pritikaselvam-svg/NovaB/02_Industrial_Design/Sketches/WhatsApp Image 2026-07-04 at 12.52.29.jpeg

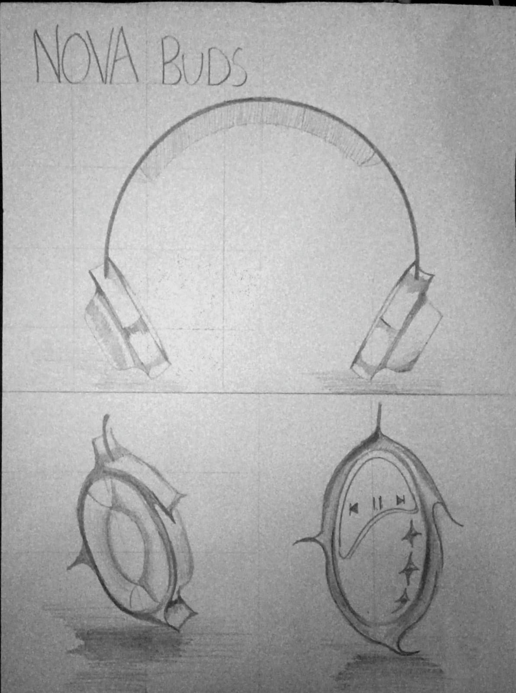
02_Industrial_Design/Sketches/WhatsApp Image 2026-07-04 at 12.52.29.jpeg
